betz-engineering/power_switch/pdf/uvlo.asc

C1: cap; 1n
C2: cap; {C_IN}
D1: zener; UMZ5_1N
M1: nmos; NDC7002N
R1: res; 470k
R2: res; 47k
R3: res; 3k
V1: voltage; PULSE(0 10 100u 1n 1n 2.5m 1 1)
Named nets: 0, power_on, rst
.tran 5m
.param C_IN 10n
.step param C_IN list 100n 2n
